Ericlinsechs/Carmax_AutoTest_Module/CAD/hex-spacer-standoff_m2-5_CAD/hex spacer standoff_M2_5 SW4 L5-L25.png

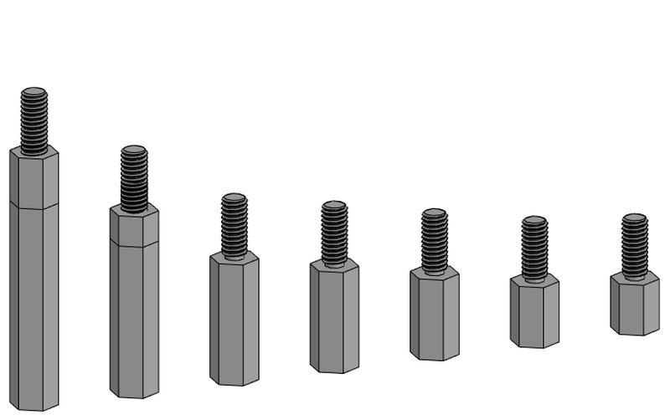
CAD/hex-spacer-standoff_m2-5_CAD/hex spacer standoff_M2_5 SW4 L5-L25.png
