Ericlinsechs/Carmax_AutoTest_Module/CAD/m3-x-25mm-socket-button-screws-allen-1.snapshot.2/m3x25.JPG

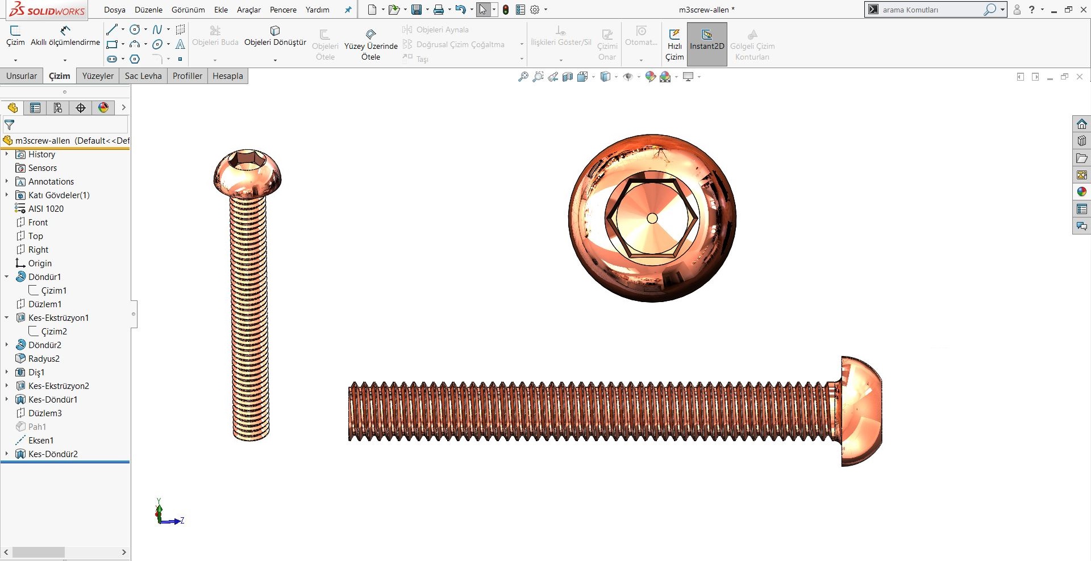
CAD/m3-x-25mm-socket-button-screws-allen-1.snapshot.2/m3x25.JPG
