Ericlinsechs/Carmax_AutoTest_Module/CAD/ina219_CAD/Placa.SLDPRT

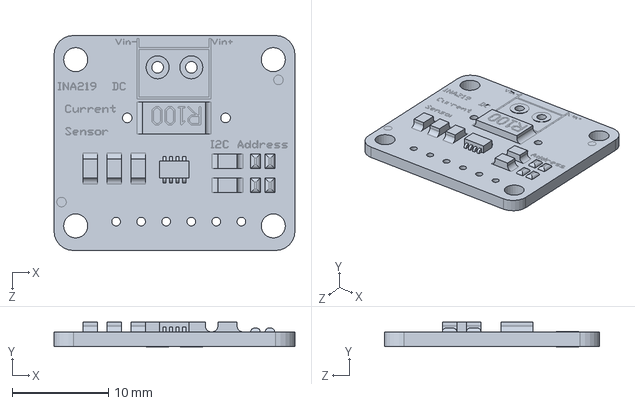
[picture p31: CAD file, 2021-05-17]
CAD/ina219_CAD/Placa.SLDPRT
25.0 x 2.56 x 22.3 mm
