Ericlinsechs/Carmax_AutoTest_Module/CAD/2-channel-5v-relay-module-1.snapshot.2/2PH63091A Parts/4 Headers.SLDPRT

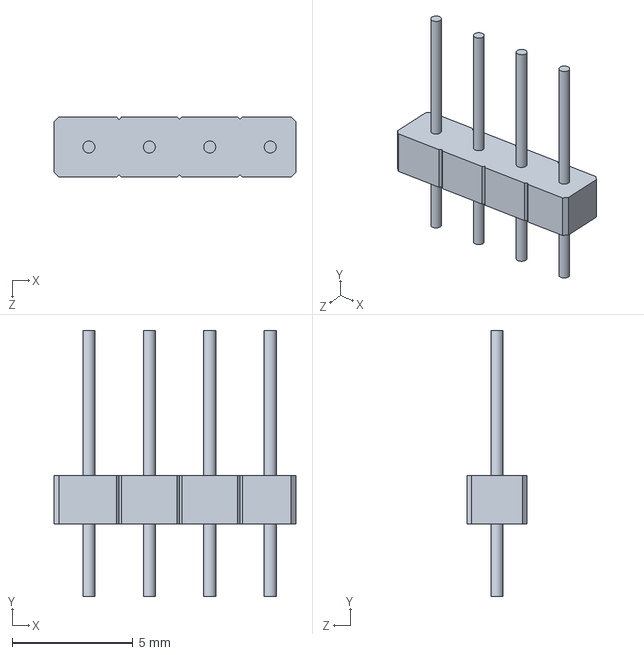
[picture p32: CAD file, 2021-06-01]
CAD/2-channel-5v-relay-module-1.snapshot.2/2PH63091A Parts/4 Headers.SLDPRT
10.0 x 11.0 x 2.50 mm
