Ericlinsechs/Carmax_AutoTest_Module/CAD/acrylic/bottom.SLDPRT

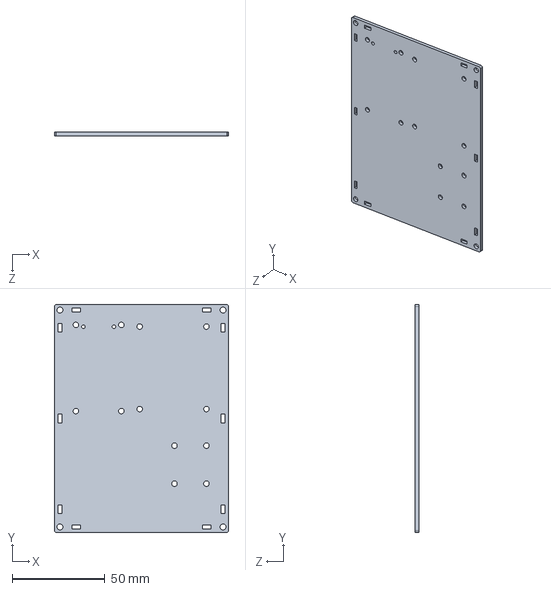
[picture p33: CAD file, 2021-06-01]
CAD/acrylic/bottom.SLDPRT
94.0 x 123.0 x 2.00 mm
