Ericlinsechs/Carmax_AutoTest_Module/CAD/Hex Nut/M2.STEP

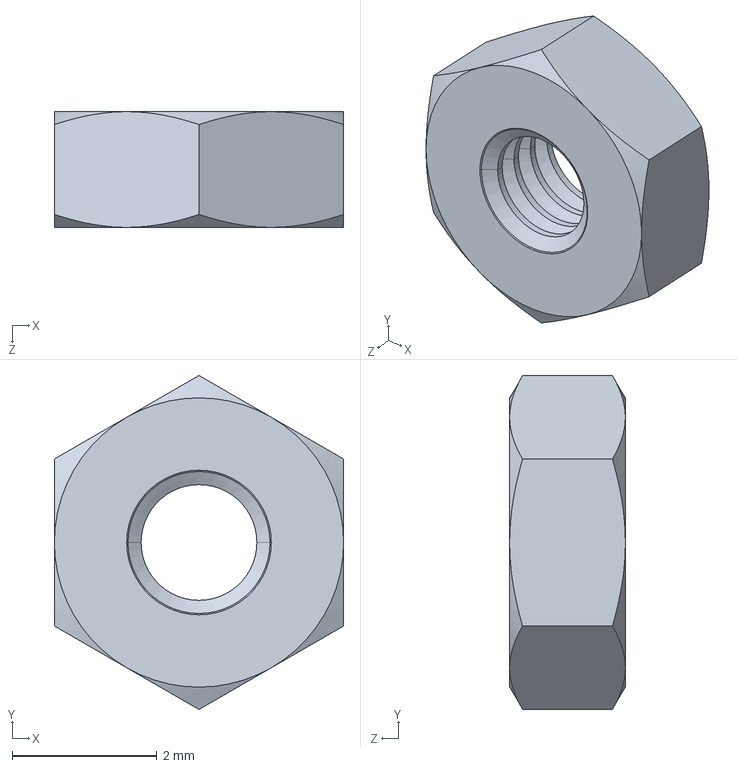
[picture p34: CAD file, 2021-05-21]
CAD/Hex Nut/M2.STEP
4.00 x 4.62 x 1.60 mm
