Ericlinsechs/Carmax_AutoTest_Module/CAD/hex-spacer-standoff_m2-5_CAD/hex spacer standoff_M2_5 SW4 L10.stp

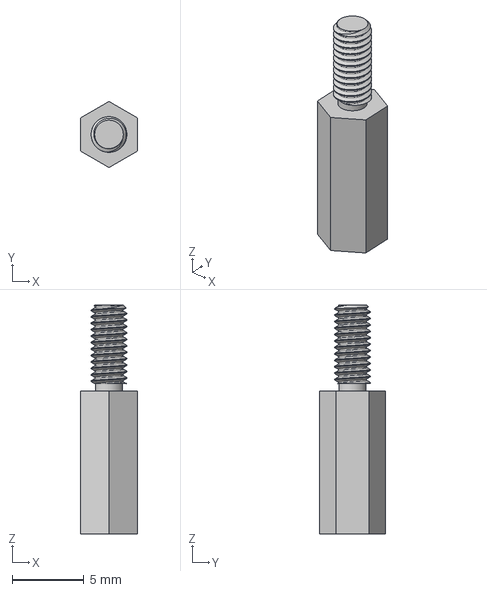
[picture p35: CAD file, 2021-05-17]
CAD/hex-spacer-standoff_m2-5_CAD/hex spacer standoff_M2_5 SW4 L10.stp
4.00 x 4.62 x 16.0 mm
