Ericlinsechs/Carmax_AutoTest_Module/CAD/ina219_CAD/INA219.STEP

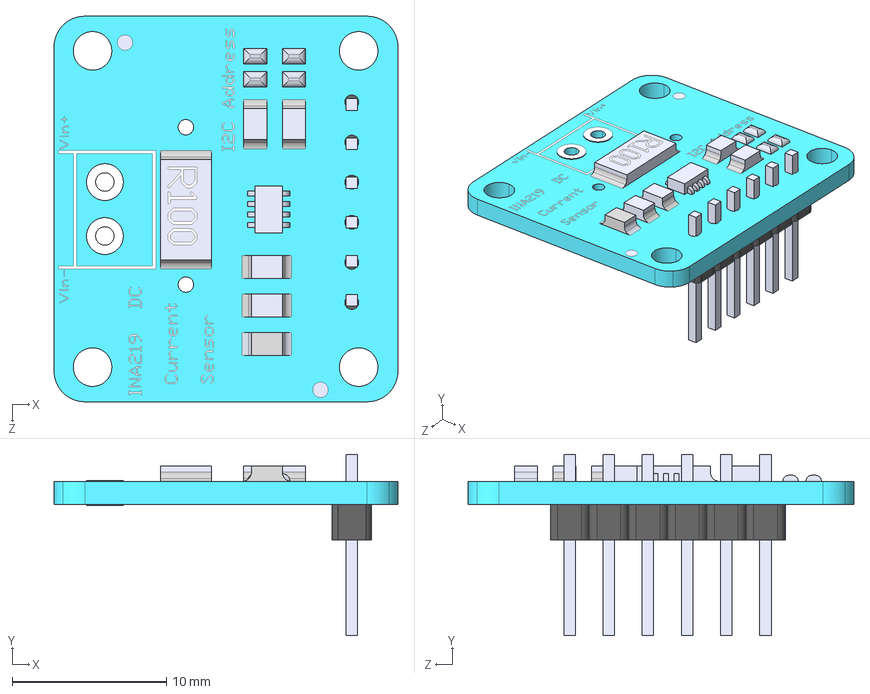
[picture p36: CAD file, 2021-05-17]
CAD/ina219_CAD/INA219.STEP
22.3 x 11.8 x 25.0 mm
6 Header-Pin
Placa
