Ericlinsechs/Carmax_AutoTest_Module/CAD/terminal_block_6.stp

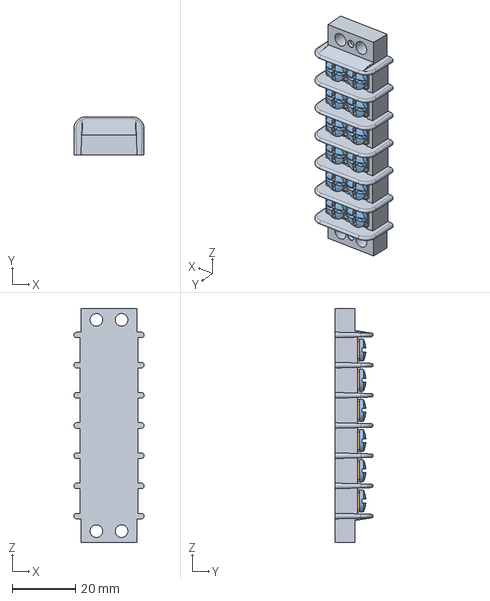
[picture p37: CAD file, 2021-05-12]
CAD/terminal_block_6.stp
22.2 x 12.1 x 73.8 mm
