Ericlinsechs/Carmax_AutoTest_Module/CAD/2-channel-5v-relay-module-1.snapshot.2/2PH63091A Parts/Clamp Body.SLDPRT

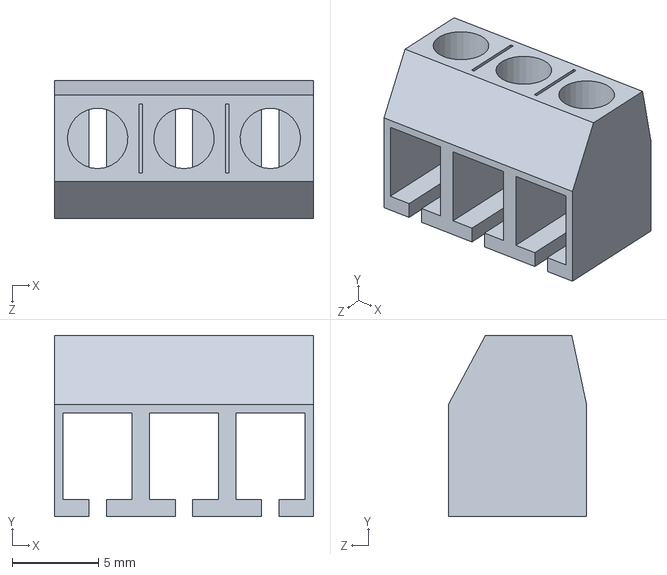
[picture p38: CAD file, 2021-06-01]
CAD/2-channel-5v-relay-module-1.snapshot.2/2PH63091A Parts/Clamp Body.SLDPRT
15.0 x 10.5 x 8.00 mm
