Ericlinsechs/Carmax_AutoTest_Module/CAD/acrylic/frontside_wall.SLDPRT

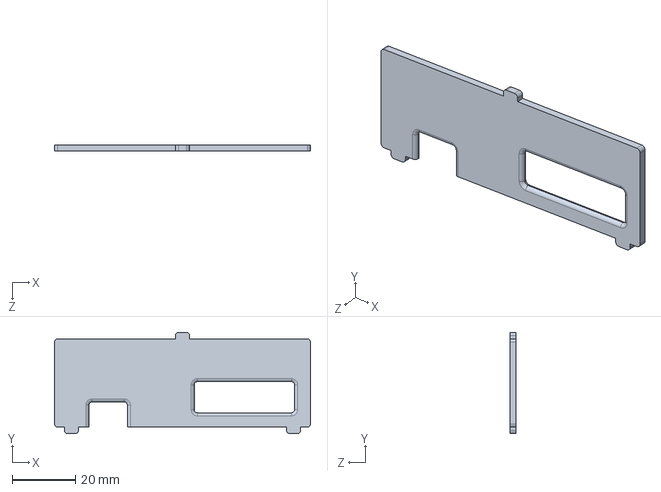
[picture p39: CAD file, 2021-06-01]
CAD/acrylic/frontside_wall.SLDPRT
81.0 x 32.0 x 2.00 mm
