Ericlinsechs/Carmax_AutoTest_Module/CAD/Hex Nut/M3.STEP

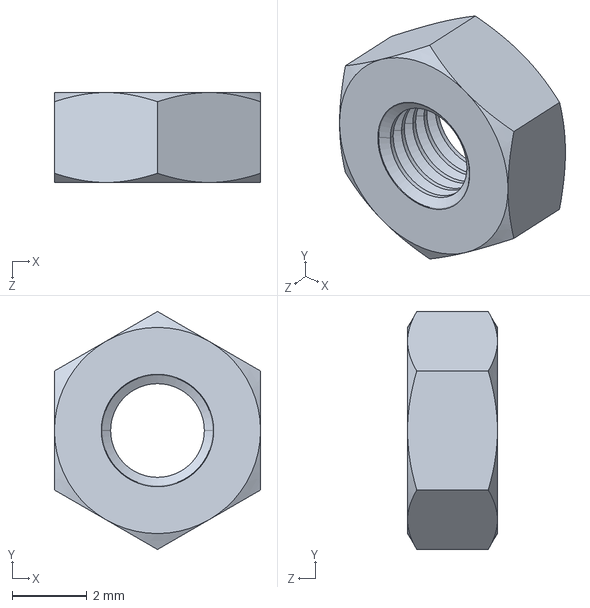
[picture p40: CAD file, 2021-05-21]
CAD/Hex Nut/M3.STEP
5.50 x 6.35 x 2.40 mm
