Ericlinsechs/Carmax_AutoTest_Module/CAD/RelayBoard.STEP

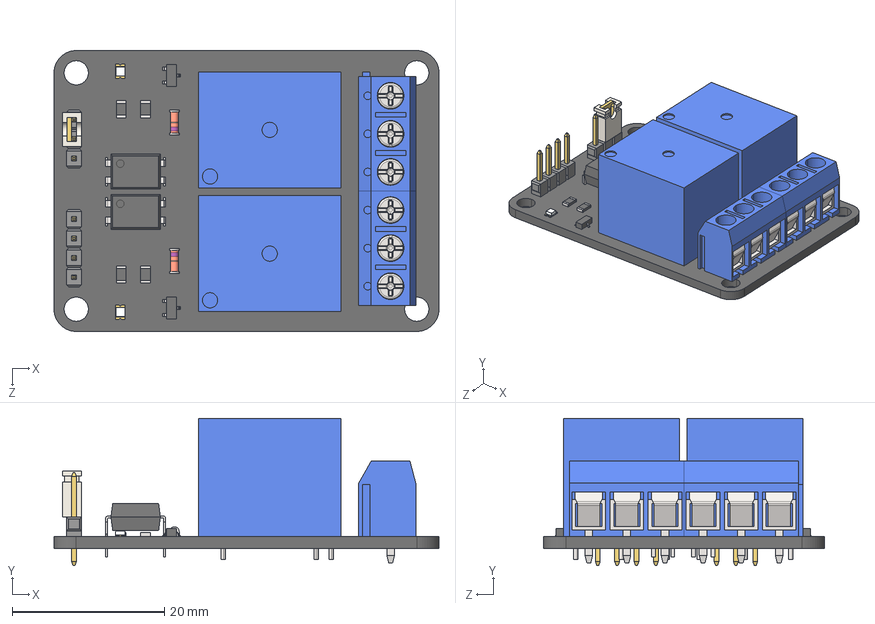
[picture p42: CAD file, 2021-05-12]
CAD/RelayBoard.STEP
50.5 x 19.3 x 36.9 mm
RelayBase
Terminator x 2
D1 x 2
sot-23-j3y x 2
Jumper
PC-817 x 2
Relay x 2
smdres_102 x 2
smdres_115 x 2
BreakAwayHeaders_3PinShort
BreakAwayHeaders_4PinShort
smallled_SmallRelay x 2
