Ericlinsechs/Carmax_AutoTest_Module/CAD/2-channel-5v-relay-module-1.snapshot.2/2PH63091A Parts/Metal Clamp Part.SLDPRT

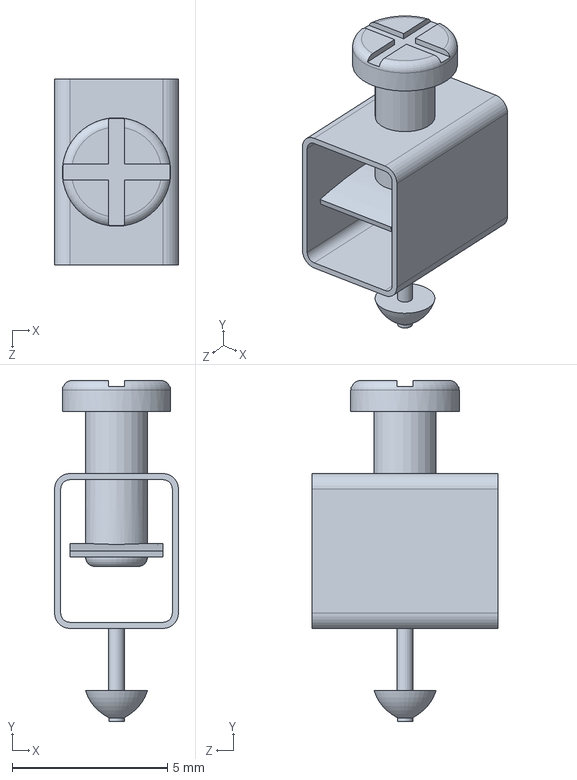
[picture p43: CAD file, 2021-06-01]
CAD/2-channel-5v-relay-module-1.snapshot.2/2PH63091A Parts/Metal Clamp Part.SLDPRT
4.00 x 11.0 x 6.00 mm
