Ericlinsechs/Carmax_AutoTest_Module/CAD/4-digit 7-segment-display module for Arduino v1.step

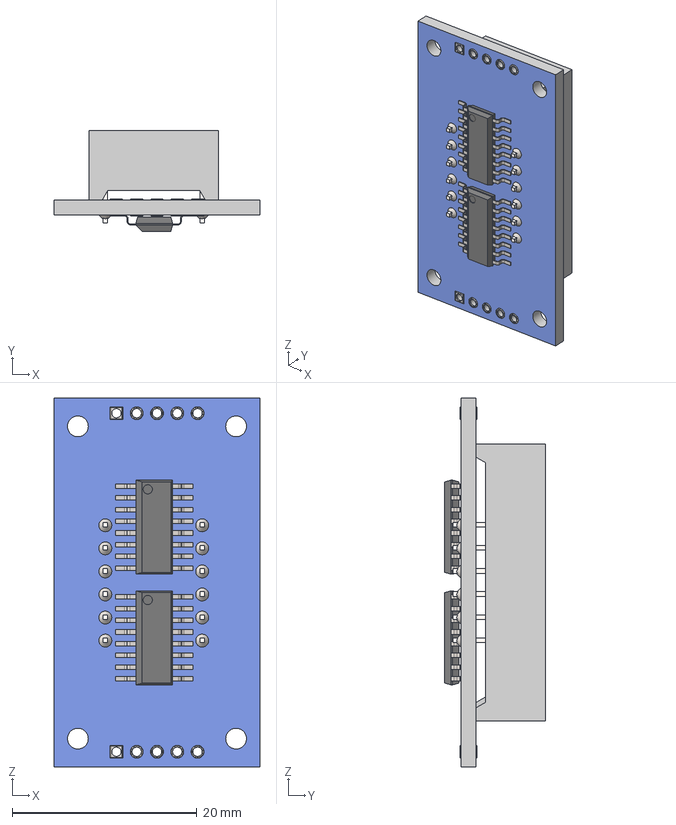
[picture p44: CAD file, 2021-05-12]
CAD/4-digit 7-segment-display module for Arduino v1.step
22.3 x 10.9 x 40.0 mm
Board^4-digit 7-segment-display module for Arduino
4-bit indicator f3461ah
tm74hc595 x 2
