Ericlinsechs/Carmax_AutoTest_Module/CAD/Hex Nut/M5.STEP

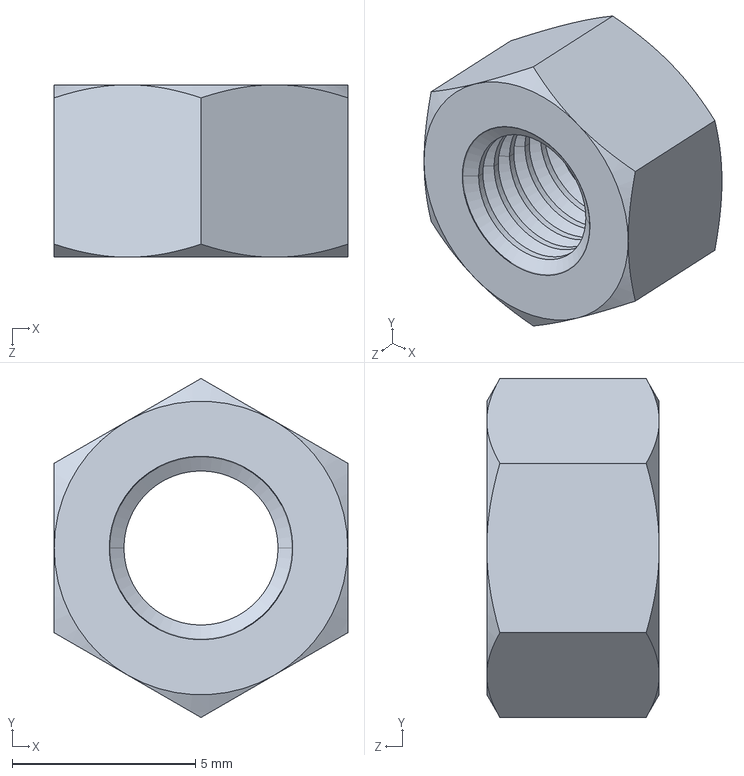
[picture p45: CAD file, 2021-05-21]
CAD/Hex Nut/M5.STEP
8.00 x 9.24 x 4.70 mm
