Ericlinsechs/Carmax_AutoTest_Module/CAD/hex-spacer-standoff_m2-5_CAD/hex spacer standoff_M2_5 SW4 L8.stp

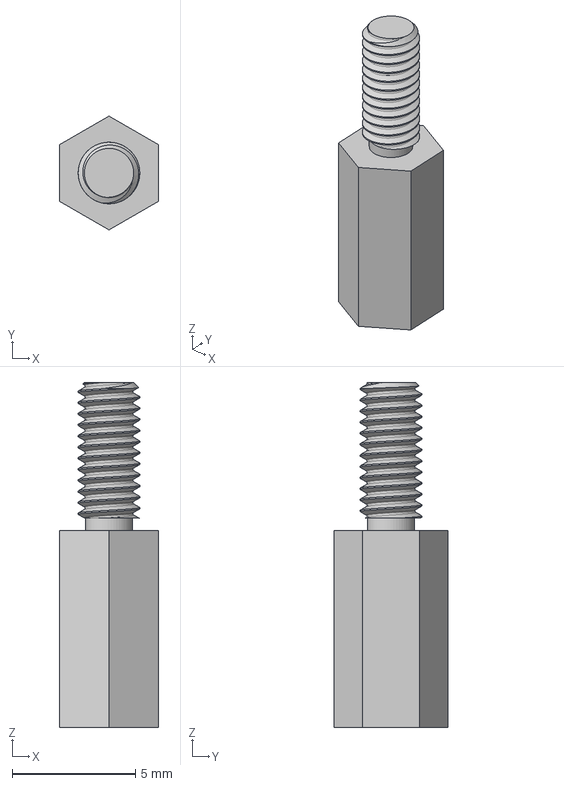
[picture p46: CAD file, 2021-05-17]
CAD/hex-spacer-standoff_m2-5_CAD/hex spacer standoff_M2_5 SW4 L8.stp
4.00 x 4.62 x 14.0 mm
