Ericlinsechs/Carmax_AutoTest_Module/CAD/2-channel-5v-relay-module-1.snapshot.2/2PH63091A Parts/Headers.SLDPRT

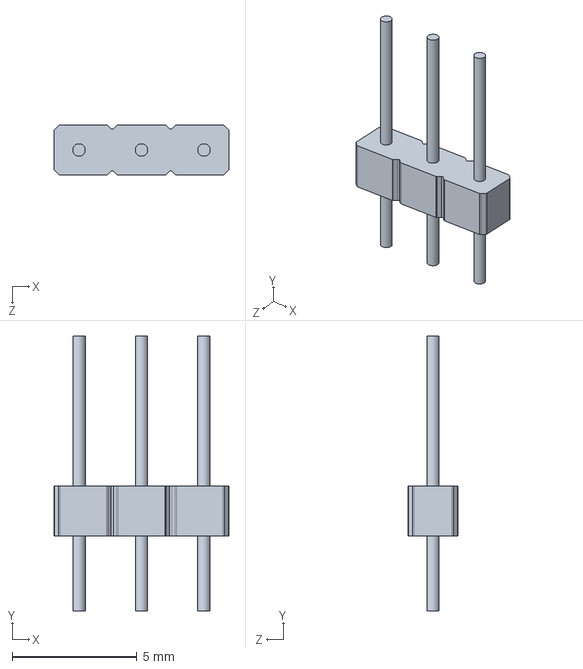
[picture p47: CAD file, 2021-06-01]
CAD/2-channel-5v-relay-module-1.snapshot.2/2PH63091A Parts/Headers.SLDPRT
7.00 x 11.0 x 2.00 mm
