Ericlinsechs/Carmax_AutoTest_Module/CAD/Hex Nut/M10.STEP

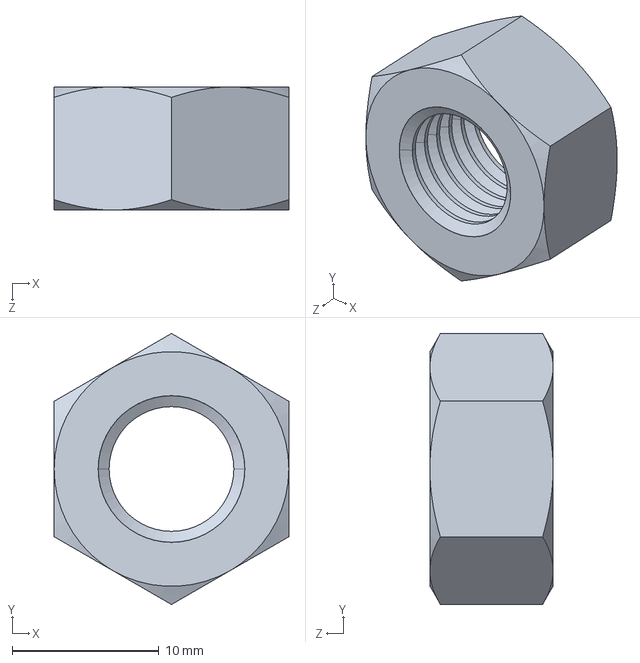
[picture p48: CAD file, 2021-05-21]
CAD/Hex Nut/M10.STEP
16.0 x 18.5 x 8.40 mm
