Ericlinsechs/Carmax_AutoTest_Module/CAD/2-channel-5v-relay-module-1.snapshot.2/2PH63091A Parts/Relay Body.SLDPRT

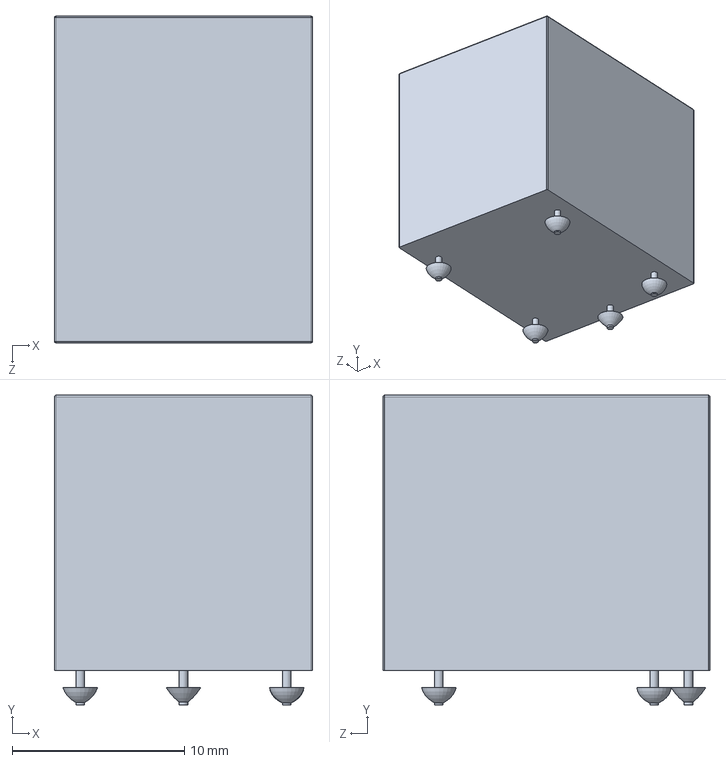
[picture p50: CAD file, 2021-06-01]
CAD/2-channel-5v-relay-module-1.snapshot.2/2PH63091A Parts/Relay Body.SLDPRT
15.0 x 18.0 x 19.0 mm
