Ericlinsechs/Carmax_AutoTest_Module/CAD/Hex Nut/M6.STEP

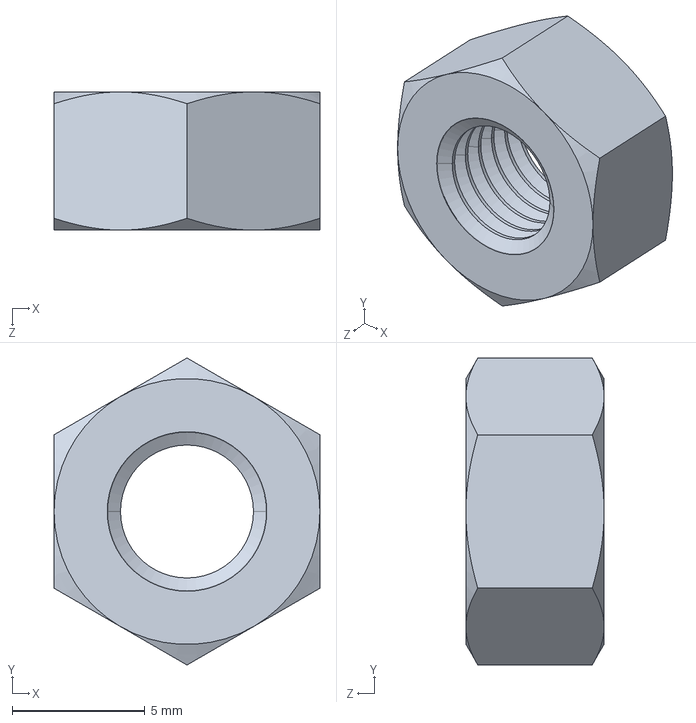
[picture p51: CAD file, 2021-05-21]
CAD/Hex Nut/M6.STEP
10.0 x 11.5 x 5.20 mm
