Ericlinsechs/Carmax_AutoTest_Module/CAD/hex-spacer-standoff_m2-5_CAD/hex spacer standoff_M2_5 SW4 L5.stp

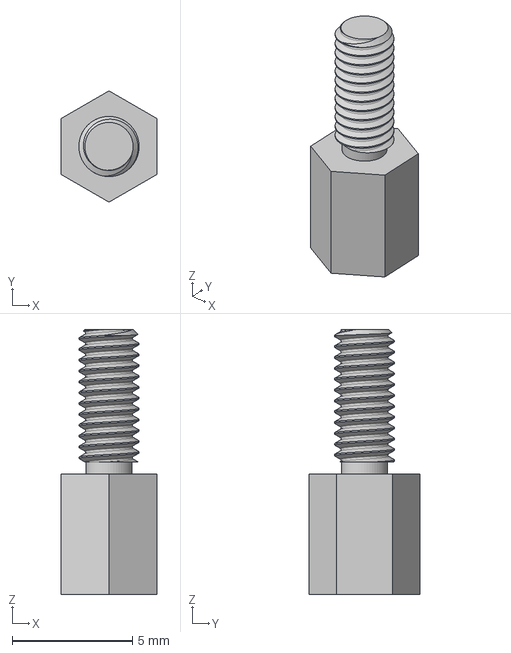
[picture p52: CAD file, 2021-05-17]
CAD/hex-spacer-standoff_m2-5_CAD/hex spacer standoff_M2_5 SW4 L5.stp
4.00 x 4.62 x 11.0 mm
