Ericlinsechs/Carmax_AutoTest_Module/circuit/autotest_module/autotest_module.sch

## KiCad design circuit/autotest_module/autotest_module.sch (2021-06-18, an earlier design)

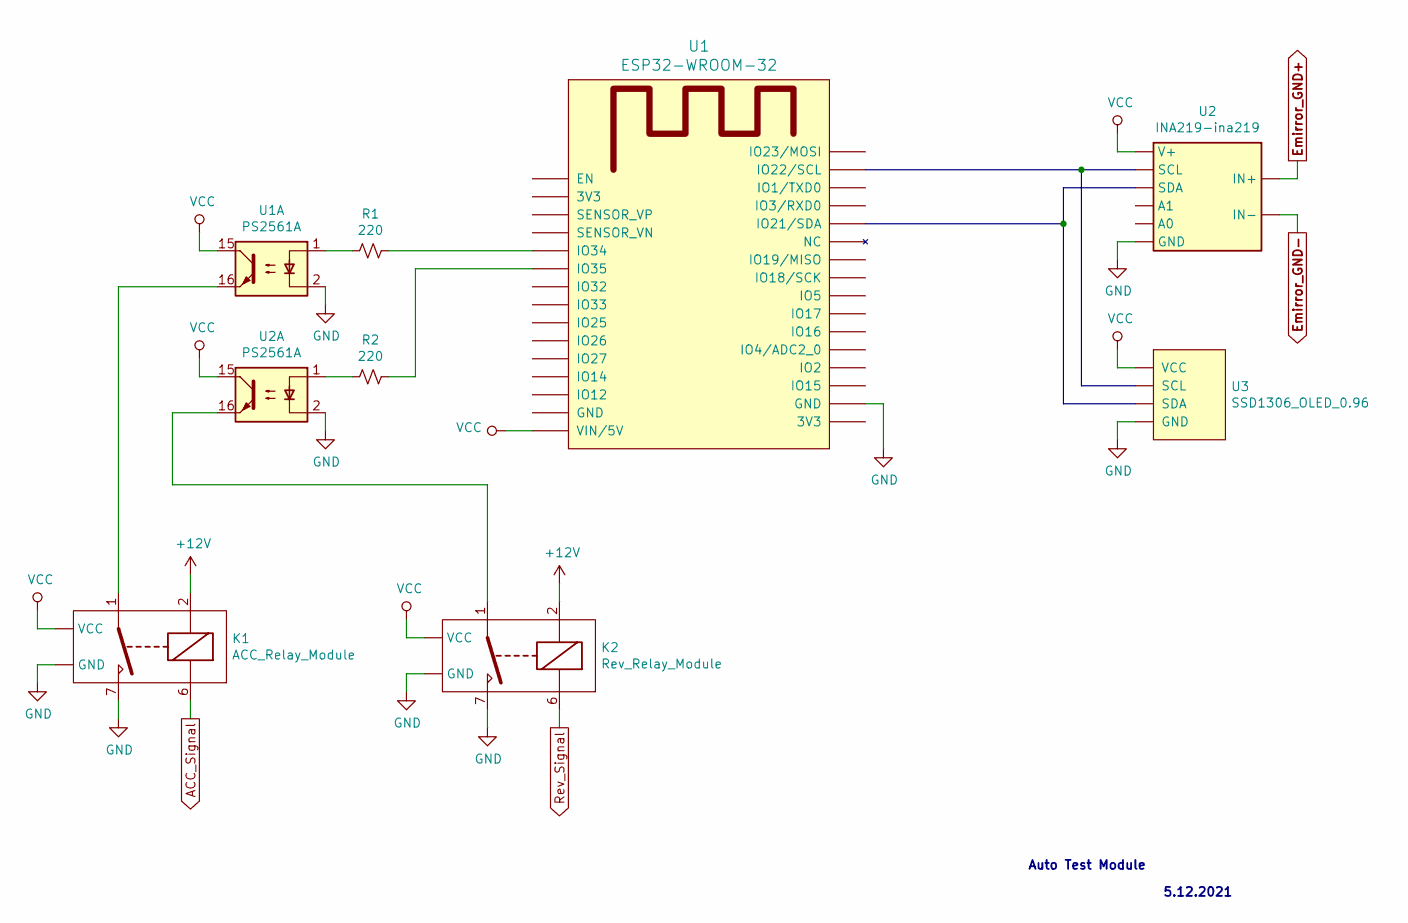
[picture p55: schematic autotest_module.sch]

Parts:
K1: ACC_Relay_Module; Relay_StandexMeder_DIP_LowProfile
K2: Rev_Relay_Module; Relay_StandexMeder_DIP_LowProfile
R1, R2: 220
U1: PS2561A
U2: INA219-ina219; SOIC-8_3.9x4.9mm_P1.27mm
U3: SSD1306_OLED_0.96

Connections:
+12V: K1.2, K2.2
ACC_Signal: K1.6
Emirror_GND+: U2.~ (A0)
Emirror_GND-: U2.~ (A0)
GND: K1.7, K1.8, K1.~ (GND), K2.7, K2.8, K2.~ (GND), U1.2 (3V3), U1.~ (3V3), U2.2, U2.~ (A0), U3.~
unnamed: K1.1, K1.14, U1.16
unnamed: K2.1, K2.14, U2.16
unnamed: R1.1, U1.1 (GND)
unnamed: R1.2, U1.6 (IO34)
unnamed: R2.1, U2.1
unnamed: R2.2, U1.7 (IO35)
Rev_Signal: K2.6
VCC: K1.~ (GND), K2.~ (GND), U1.15, U1.~ (3V3), U2.15, U2.~ (A0), U3.~

Notes on the sheet:
Auto Test Module
5.12.2021
